bkw777/rgb2vga/pcb/out/COCO3_pins.jpg

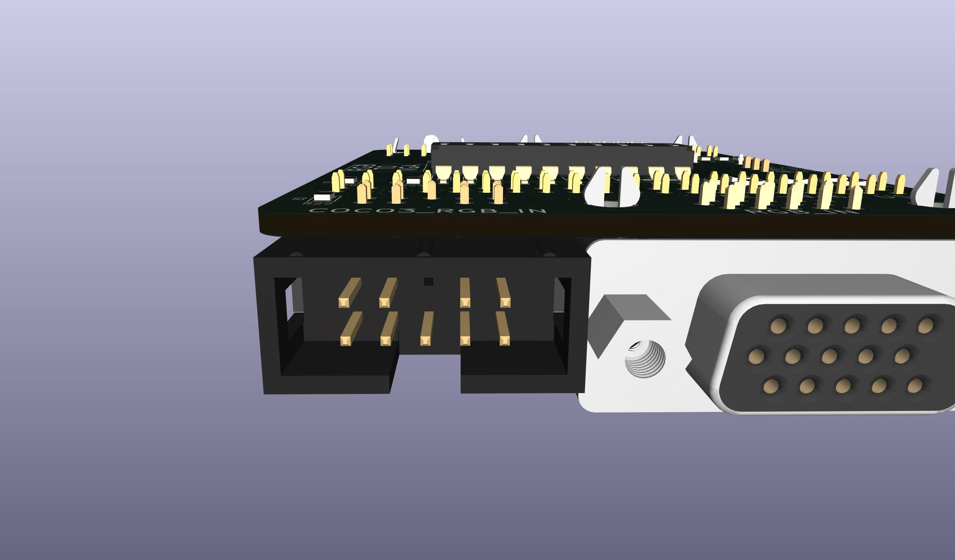
pcb/out/COCO3_pins.jpg
