bkw777/rgb2vga/pics/rgb2vga_1.jpg

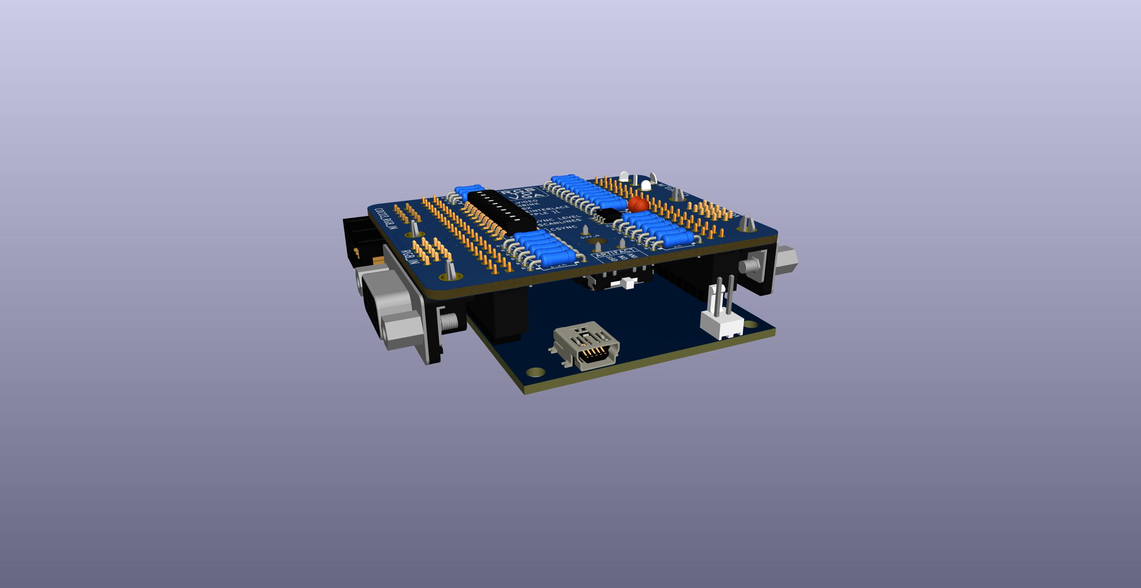
pics/rgb2vga_1.jpg
