bkw777/rgb2vga/pics/rgb2vga_2.jpg

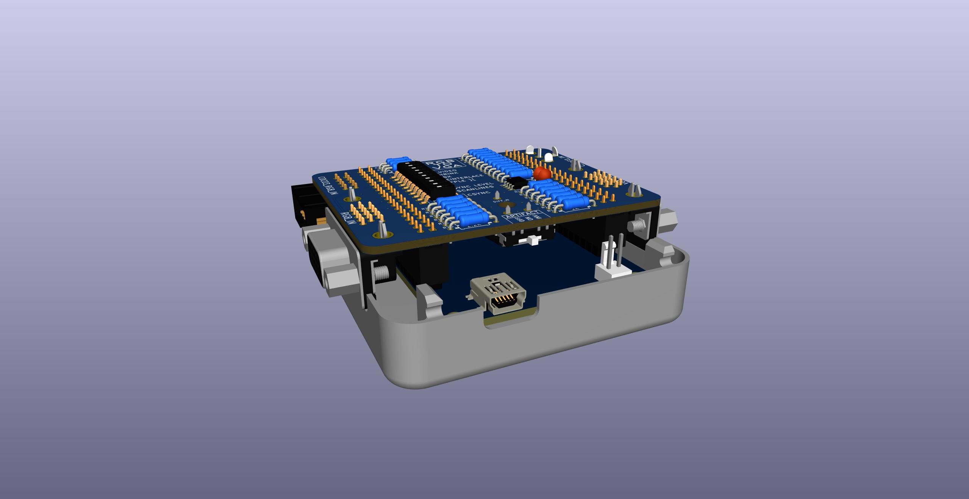
pics/rgb2vga_2.jpg
