bkw777/rgb2vga/pics/rgb2vga_6.jpg

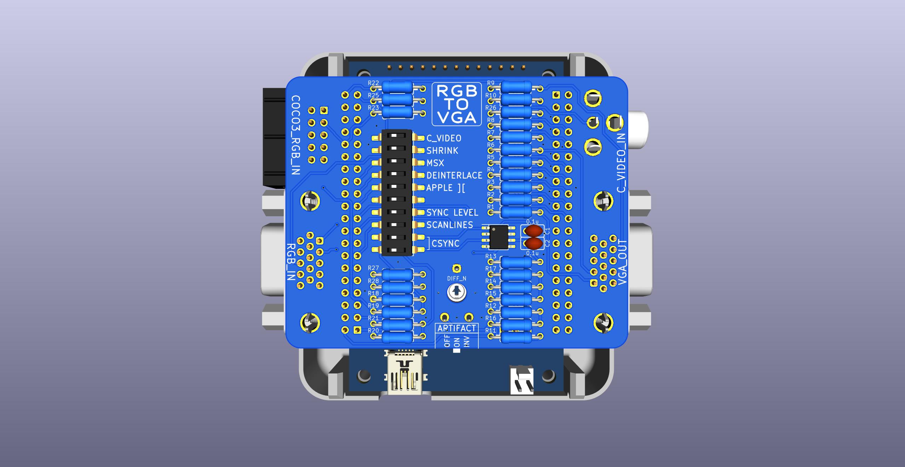
pics/rgb2vga_6.jpg
