bkw777/rgb2vga/pics/rgb2vga_7.jpg

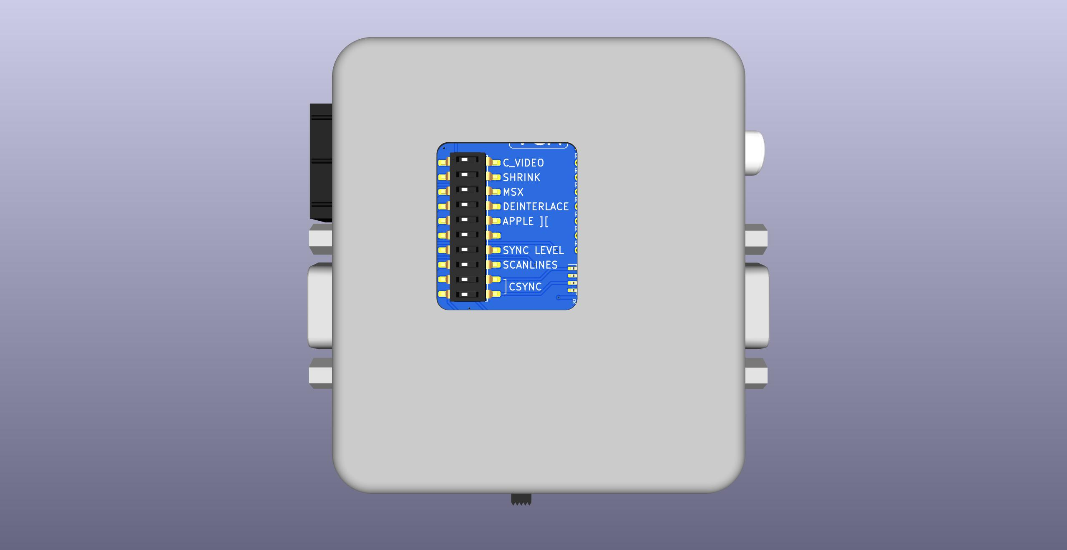
pics/rgb2vga_7.jpg
