bkw777/rgb2vga/pics/rgb2vga_8.jpg

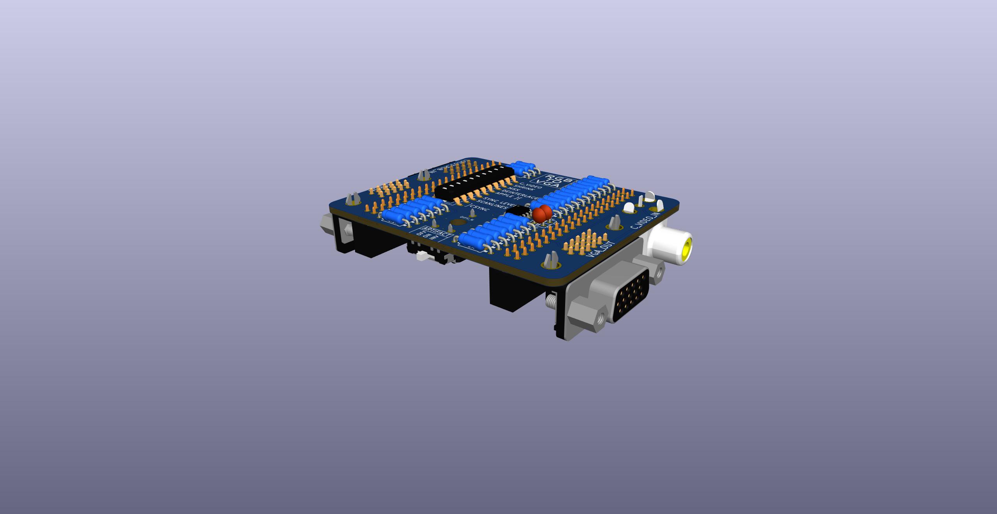
pics/rgb2vga_8.jpg
