bkw777/rgb2vga/pics/rgb2vga_12.jpg

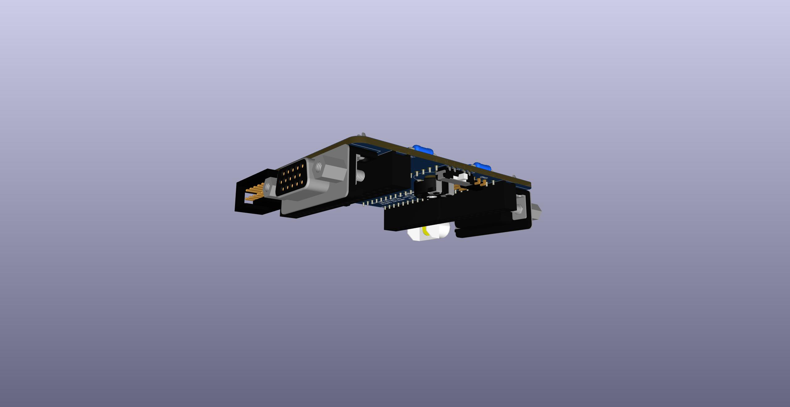
pics/rgb2vga_12.jpg
