bkw777/rgb2vga/ref/Ed_Snider_PCB_Roger_Taylor_resistors.jpg

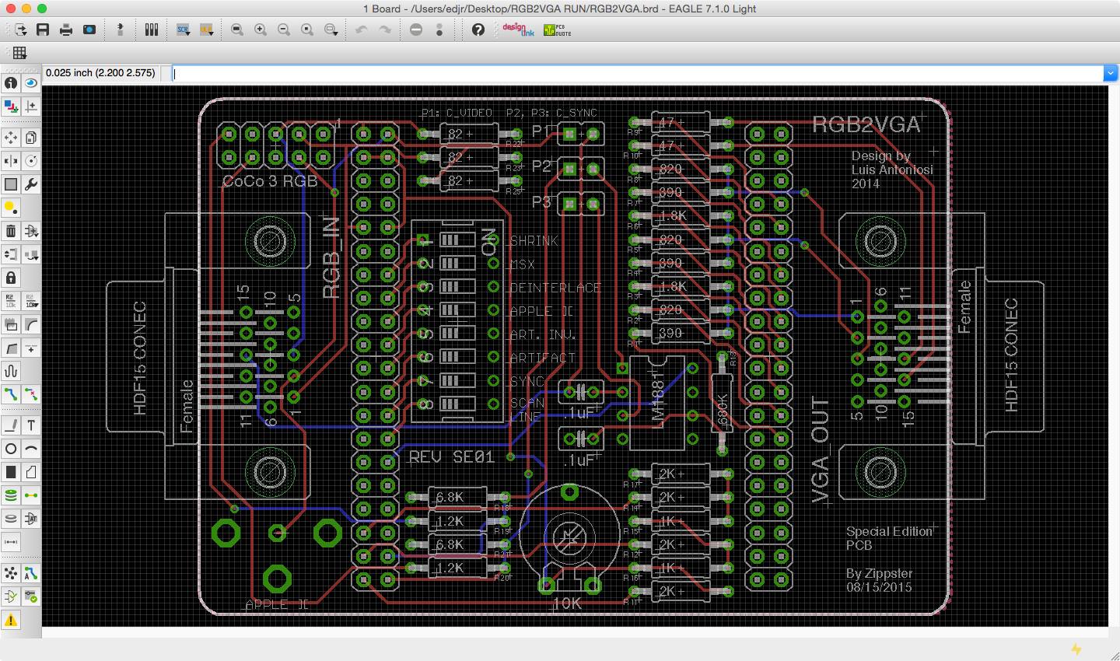
ref/Ed_Snider_PCB_Roger_Taylor_resistors.jpg
