bkw777/rgb2vga/ref/EdSnider_pcb_photo.jpg

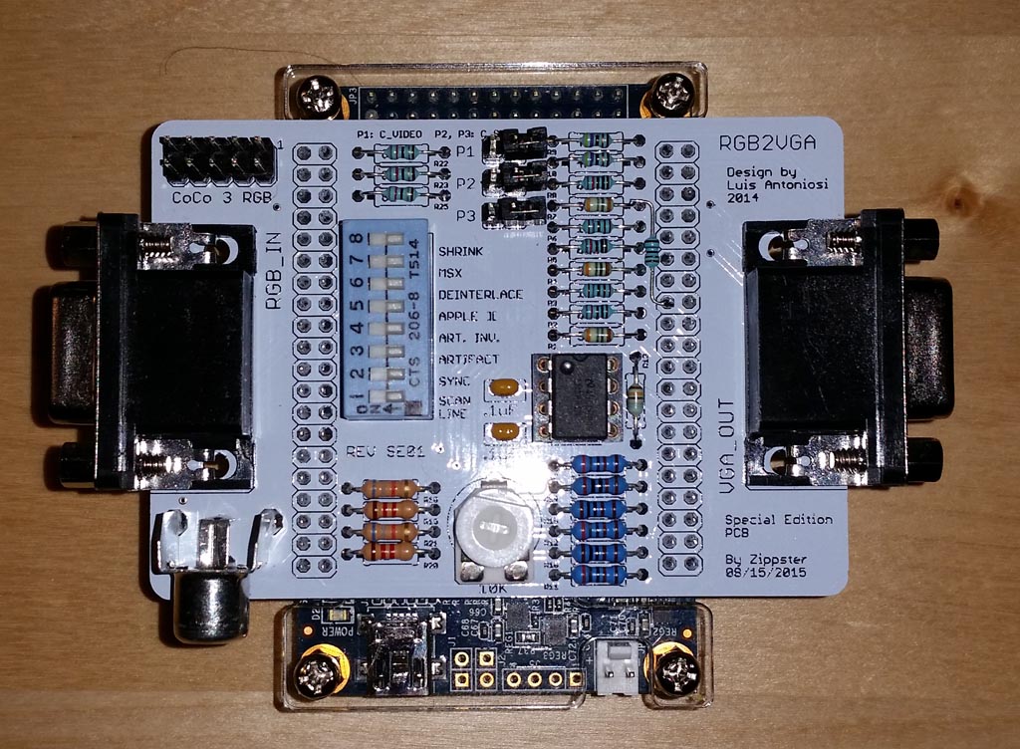
ref/EdSnider_pcb_photo.jpg
