bkw777/rgb2vga/ref/new_resistors2.png

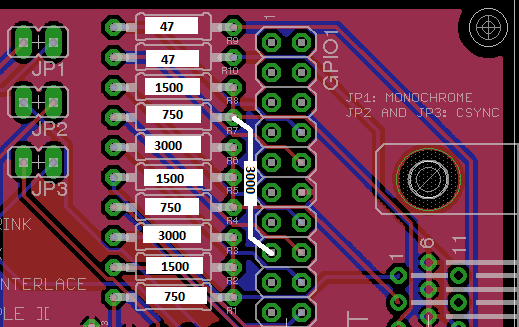
ref/new_resistors2.png
